GarrettBBoyd/PicoGameCubeMacroTool/firmware/src/btstack_config.h

#ifndef BTSTACK_CONFIG_H
#define BTSTACK_CONFIG_H

// BLE only
#ifndef ENABLE_BLE
#define ENABLE_BLE
#endif
#define ENABLE_LE_PERIPHERAL
#define ENABLE_L2CAP_LE_CREDIT_BASED_FLOW_CONTROL_MODE

// CYW43 transport requirements
#define HCI_OUTGOING_PRE_BUFFER_SIZE 4
#define HCI_ACL_CHUNK_SIZE_ALIGNMENT 4

// Buffer configuration
#define MAX_ATT_DB_SIZE 512
#define HCI_ACL_PAYLOAD_SIZE (1691 + 4)
#define HCI_INCOMING_PRE_BUFFER_SIZE 6

// Flow control for CYW43 shared bus
#define MAX_NR_CONTROLLER_ACL_BUFFERS 3
#define MAX_NR_CONTROLLER_SCO_PACKETS 3
#define ENABLE_HCI_CONTROLLER_TO_HOST_FLOW_CONTROL
#define HCI_HOST_ACL_PACKET_LEN 1024
#define HCI_HOST_ACL_PACKET_NUM 3
#define HCI_HOST_SCO_PACKET_LEN 120
#define HCI_HOST_SCO_PACKET_NUM 3

// Connection limits
#define MAX_NR_HCI_CONNECTIONS 2
#define MAX_NR_L2CAP_CHANNELS 4
#define MAX_NR_GATT_CLIENTS 1
#define MAX_NR_LE_DEVICE_DB_ENTRIES 4
#define NVM_NUM_DEVICE_DB_ENTRIES 4
#define NVM_NUM_LINK_KEYS 4

// Crypto
#define ENABLE_SOFTWARE_AES128

// Platform
#define HAVE_EMBEDDED_TIME_MS

// Logging
#define ENABLE_LOG_ERROR
#define ENABLE_PRINTF_HEXDUMP
// #define ENABLE_LOG_INFO

#endif
